Colatino/PicoZoom/src/beta/a1xfour.h

/*
 * The MIT License (MIT)
 *
 * Copyright (c) 2022 André Colatino (https://github.com/Colatino/picozoom)
 *
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
 * This file is part of the PicoZoom project.
 */

#ifndef A1XFOUR_H
#define A1XFOUR_H
#include "effect_model.h"

#define NEFFECTS 199
#define NUM_SLOTS 5
#define NUM_PEDALS 5

#define PEDAL_ID 0x6e
#define N_DELAYS 18
long delay_ids[] = { 138412032, 134217761, 134217937, 134217745, 134217889, 134217872, 134217985, 134217808, 144707584, 134217953, 134217857, 134217905, 134217793, 134218001, 134217921, 134218017, 134217776, 134217969 };

Effect effects[NEFFECTS] = {
  { "Bypass", 0, "", 1, 0, { { 0, 0, 0, 0, "-" }, { 0, 0, 0, 0, "-" }, { 0, 0, 0, 0, "-" }, { 0, 0, 0, 0, "-" }, { 0, 0, 0, 0, "-" }, { 0, 0, 0, 0, "-" }, { 0, 0, 0, 0, "-" }, { 0, 0, 0, 0, "-" } } },
  { "160 Comp", 25165872, "160_COMP.ZD2.BMP", 1, 4, { { 0, 60, 38, 0, "THRSH" }, { 0, 90, 30, 0, "Ratio" }, { 0, 1, 1, 0, "Knee" }, { 0, 100, 80, 0, "VOL" }, { 0, 0, 0, 0, "-" }, { 0, 0, 0, 0, "-" }, { 0, 0, 0, 0, "-" }, { 0, 0, 0, 0, "-" } } },
  { "AG Detune", 104857600, "ACDETUNE.ZD2.BMP", 1, 4, { { 0, 25, 12, 0, "Cent" }, { 0, 50, 34, 0, "PreD" }, { 0, 100, 50, 0, "Tone" }, { 0, 100, 50, 0, "Mix" }, { 0, 0, 0, 0, "-" }, { 0, 0, 0, 0, "-" }, { 0, 0, 0, 0, "-" }, { 0, 0, 0, 0, "-" } } },
  { "Ac TpEcho", 138412032, "AC_TPECH.ZD2.BMP", 1, 4, { { 0, 1005, 350, 0, "Time" }, { 0, 100, 20, 0, "F.B" }, { 0, 100, 50, 0, "Mix" }, { 0, 1, 0, 0, "Tail" }, { 0, 0, 0, 0, "-" }, { 0, 0, 0, 0, "-" }, { 0, 0, 0, 0, "-" }, { 0, 0, 0, 0, "-" } } },
  { "AG Chorus", 104857616, "AC_TRCHO.ZD2.BMP", 1, 4, { { 0, 100, 29, 0, "Speed" }, { 0, 100, 80, 0, "Depth" }, { 0, 100, 100, 0, "Tone" }, { 0, 100, 41, 0, "Mix" }, { 0, 0, 0, 0, "-" }, { 0, 0, 0, 0, "-" }, { 0, 0, 0, 0, "-" }, { 0, 0, 0, 0, "-" } } },
  { "Adv.NR", 27267072, "ADVNR.ZD2.BMP", 1, 4, { { 0, 100, 30, 0, "THRSH" }, { 0, 100, 0, 0, "ATTCK" }, { 0, 100, 0, 0, "Hold" }, { 0, 100, 80, 0, "Decay" }, { 0, 0, 0, 0, "-" }, { 0, 0, 0, 0, "-" }, { 0, 0, 0, 0, "-" }, { 0, 0, 0, 0, "-" } } },
  { "AG PU SEL", 37748737, "AG_PUSL.ZD2.BMP", 1, 1, { { 0, 1, 0, 0, "Type" }, { 0, 0, 0, 0, "-" }, { 0, 0, 0, 0, "-" }, { 0, 0, 0, 0, "-" }, { 0, 0, 0, 0, "-" }, { 0, 0, 0, 0, "-" }, { 0, 0, 0, 0, "-" }, { 0, 0, 0, 0, "-" } } },
  { "Air", 150994960, "AIR.ZD2.BMP", 1, 4, { { 0, 99, 19, 0, "Size" }, { 0, 10, 5, 0, "REF" }, { 0, 100, 60, 0, "Mix" }, { 0, 1, 0, 0, "Tail" }, { 0, 0, 0, 0, "-" }, { 0, 0, 0, 0, "-" }, { 0, 0, 0, 0, "-" }, { 0, 0, 0, 0, "-" } } },
  { "AnalogCho", 100663632, "ANA234CH.ZD2.BMP", 1, 4, { { 0, 100, 52, 0, "Depth" }, { 0, 100, 54, 0, "Rate" }, { 0, 100, 49, 0, "Tone" }, { 0, 100, 82, 0, "Mix" }, { 0, 0, 0, 0, "-" }, { 0, 0, 0, 0, "-" }, { 0, 0, 0, 0, "-" }, { 0, 0, 0, 0, "-" } } },
  { "AnalogDly", 134217761, "ANDLY_3S.ZD2.BMP", 1, 4, { { 0, 3018, 359, 0, "Time" }, { 0, 100, 28, 0, "F.B" }, { 0, 100, 40, 0, "Mix" }, { 0, 1, 0, 0, "Tail" }, { 0, 0, 0, 0, "-" }, { 0, 0, 0, 0, "-" }, { 0, 0, 0, 0, "-" }, { 0, 0, 0, 0, "-" } } },
  { "Anti FB", 50331632, "ANTI_FB.ZD2.BMP", 1, 1, { { 0, 139, 0, 0, "FREQ" }, { 0, 0, 0, 0, "-" }, { 0, 0, 0, 0, "-" }, { 0, 0, 0, 0, "-" }, { 0, 0, 0, 0, "-" }, { 0, 0, 0, 0, "-" }, { 0, 0, 0, 0, "-" }, { 0, 0, 0, 0, "-" } } },
  { "A-Pan DLY", 134217937, "APANDL3S.ZD2.BMP", 2, 7, { { 0, 1512, 222, 0, "Time" }, { 0, 100, 87, 0, "F.B" }, { 0, 100, 53, 0, "Mix" }, { 0, 1, 1, 0, "Link" }, { 0, 52, 26, 0, "Cycle" }, { 0, 50, 50, 0, "Width" }, { 0, 10, 0, 0, "Clip" }, { 0, 0, 0, 0, "-" } } },
  { "SaxAtkFlt", 44041236, "ATK_FLT.ZD2.BMP", 2, 8, { { 0, 9, 7, 0, "Sense" }, { 0, 9, 7, 0, "RESO" }, { 0, 100, 80, 0, "BAL" }, { 0, 2, 0, 0, "SW" }, { 0, 77, 54, 0, "Rate" }, { 0, 3, 0, 0, "Wave" }, { 0, 1, 0, 0, "Range" }, { 0, 100, 80, 0, "VOL" } } },
  { "AutoPan", 117440544, "AUTOPAN.ZD2.BMP", 1, 4, { { 0, 78, 5, 0, "Rate" }, { 0, 50, 50, 0, "Width" }, { 0, 10, 0, 0, "Clip" }, { 0, 100, 80, 0, "VOL" }, { 0, 0, 0, 0, "-" }, { 0, 0, 0, 0, "-" }, { 0, 0, 0, 0, "-" }, { 0, 0, 0, 0, "-" } } },
  { "AutoWah", 33554448, "AUTOWAH.ZD2.BMP", 1, 4, { { 0, 1, 1, 0, "Mode" }, { 0, 9, 7, 0, "Sense" }, { 0, 10, 8, 0, "RESO" }, { 0, 100, 80, 0, "VOL" }, { 0, 0, 0, 0, "-" }, { 0, 0, 0, 0, "-" }, { 0, 0, 0, 0, "-" }, { 0, 0, 0, 0, "-" } } },
  { "Hm A.Wah", 44040546, "AWAH_HM.ZD2.BMP", 1, 4, { { 0, 9, 4, 0, "Sense" }, { 0, 10, 5, 0, "RESO" }, { 0, 100, 0, 0, "Range" }, { 0, 100, 83, 0, "BAL" }, { 0, 0, 0, 0, "-" }, { 0, 0, 0, 0, "-" }, { 0, 0, 0, 0, "-" }, { 0, 0, 0, 0, "-" } } },
  { "Sax A.Wah", 44041234, "AWAH_SAX.ZD2.BMP", 1, 4, { { 0, 9, 4, 0, "Sense" }, { 0, 10, 5, 0, "RESO" }, { 0, 100, 83, 0, "BAL" }, { 0, 1, 0, 0, "INST" }, { 0, 0, 0, 0, "-" }, { 0, 0, 0, 0, "-" }, { 0, 0, 0, 0, "-" }, { 0, 0, 0, 0, "-" } } },
  { "Tp A.Wah", 44041090, "AWAH_TP.ZD2.BMP", 2, 6, { { 0, 9, 4, 0, "Sense" }, { 0, 10, 5, 0, "RESO" }, { 0, 100, 80, 0, "BAL" }, { 0, 10, 5, 0, "THRSH" }, { 0, 10, 5, 0, "Peak" }, { 0, 100, 80, 0, "VOL" }, { 0, 0, 0, 0, "-" }, { 0, 0, 0, 0, "-" } } },
  { "Vn A.Wah", 44040836, "AWAH_VN.ZD2.BMP", 1, 4, { { 0, 19, 15, 0, "Sense" }, { 0, 10, 7, 0, "RESO" }, { 0, 10, 6, 0, "LoMix" }, { 0, 100, 100, 0, "BAL" }, { 0, 0, 0, 0, "-" }, { 0, 0, 0, 0, "-" }, { 0, 0, 0, 0, "-" }, { 0, 0, 0, 0, "-" } } },
  { "A-Filter", 41943088, "A_FILTER.ZD2.BMP", 1, 4, { { 0, 1, 0, 0, "Mode" }, { 0, 9, 7, 0, "Sense" }, { 0, 10, 7, 0, "Peak" }, { 0, 100, 10, 0, "Dry" }, { 0, 0, 0, 0, "-" }, { 0, 0, 0, 0, "-" }, { 0, 0, 0, 0, "-" }, { 0, 0, 0, 0, "-" } } },
  { "Baggs EQ", 37748784, "BAGGSEQ.ZD2.BMP", 2, 8, { { 0, 40, 20, 0, "Bass" }, { 0, 40, 20, 0, "LMidF" }, { 0, 40, 20, 0, "LoMid" }, { 0, 40, 20, 0, "HMidF" }, { 0, 40, 20, 0, "HiMid" }, { 0, 40, 20, 0, "PRSNC" }, { 0, 40, 20, 0, "TRBL" }, { 0, 100, 80, 0, "VOL" } } },
  { "BassWah", 192938000, "BASSWAH.ZD2.BMP", 1, 4, { { 1, 100, 50, 0, "FREQ" }, { 0, 100, 50, 0, "Range" }, { 0, 100, 20, 0, "Dry" }, { 0, 100, 80, 0, "VOL" }, { 0, 0, 0, 0, "-" }, { 0, 0, 0, 0, "-" }, { 0, 0, 0, 0, "-" }, { 0, 0, 0, 0, "-" } } },
  { "BassPhase", 109052032, "BASS_PHA.ZD2.BMP", 1, 4, { { 0, 1, 1, 0, "Color" }, { 0, 100, 100, 0, "Depth" }, { 0, 100, 55, 0, "Rate" }, { 0, 100, 56, 0, "RESO" }, { 0, 0, 0, 0, "-" }, { 0, 0, 0, 0, "-" }, { 0, 0, 0, 0, "-" }, { 0, 0, 0, 0, "-" } } },
  { "Bass Cry", 41943104, "BA_CRY.ZD2.BMP", 1, 4, { { 0, 9, 3, 0, "Range" }, { 0, 10, 9, 0, "RESO" }, { 0, 19, 17, 0, "Sense" }, { 0, 100, 100, 0, "BAL" }, { 0, 0, 0, 0, "-" }, { 0, 0, 0, 0, "-" }, { 0, 0, 0, 0, "-" }, { 0, 0, 0, 0, "-" } } },
  { "BassGEQ", 41943121, "BA_GEQ1U.ZD2.BMP", 2, 8, { { 0, 48, 24, 0, "50" }, { 0, 48, 24, 0, "120" }, { 0, 48, 24, 0, "400" }, { 0, 48, 24, 0, "500" }, { 0, 48, 24, 0, "800" }, { 0, 48, 24, 0, "4.5k" }, { 0, 48, 24, 0, "10k" }, { 0, 100, 80, 0, "VOL" } } },
  { "BassPEQ", 41943152, "BA_PEQ.ZD2.BMP", 1, 4, { { 0, 37, 8, 0, "FREQ" }, { 0, 67, 5, 0, "Q" }, { 0, 80, 40, 0, "Gain" }, { 0, 100, 80, 0, "VOL" }, { 0, 0, 0, 0, "-" }, { 0, 0, 0, 0, "-" }, { 0, 0, 0, 0, "-" }, { 0, 0, 0, 0, "-" } } },
  { "BendCho", 100663616, "BENDCHO.ZD2.BMP", 1, 4, { { 0, 1, 0, 0, "Mode" }, { 0, 100, 40, 0, "Depth" }, { 0, 50, 50, 0, "Time" }, { 0, 100, 100, 0, "BAL" }, { 0, 0, 0, 0, "-" }, { 0, 0, 0, 0, "-" }, { 0, 0, 0, 0, "-" }, { 0, 0, 0, 0, "-" } } },
  { "BlackOpt", 25165840, "BLACKOPT.ZD2.BMP", 1, 4, { { 0, 100, 50, 0, "Comp" }, { 0, 100, 50, 0, "Lo" }, { 0, 100, 50, 0, "Hi" }, { 0, 100, 76, 0, "VOL" }, { 0, 0, 0, 0, "-" }, { 0, 0, 0, 0, "-" }, { 0, 0, 0, 0, "-" }, { 0, 0, 0, 0, "-" } } },
  { "BlackWah", 184549408, "BLCK_WAH.ZD2.BMP", 1, 4, { { 1, 100, 50, 0, "FREQ" }, { 0, 100, 50, 0, "Range" }, { 0, 100, 0, 0, "Dry" }, { 0, 100, 80, 0, "VOL" }, { 0, 0, 0, 0, "-" }, { 0, 0, 0, 0, "-" }, { 0, 0, 0, 0, "-" }, { 0, 0, 0, 0, "-" } } },
  { "Bomber", 117440528, "BOMBER.ZD2.BMP", 1, 4, { { 0, 99, 49, 0, "Decay" }, { 0, 10, 4, 0, "Tone" }, { 0, 100, 30, 0, "Mix" }, { 0, 1, 1, 0, "ON/OFF" }, { 0, 0, 0, 0, "-" }, { 0, 0, 0, 0, "-" }, { 0, 0, 0, 0, "-" }, { 0, 0, 0, 0, "-" } } },
  { "Bone EQ", 37748800, "BONE_EQ.ZD2.BMP", 2, 8, { { 0, 40, 20, 0, "Bass" }, { 0, 40, 20, 0, "Mid F" }, { 0, 40, 20, 0, "Mid" }, { 0, 40, 20, 0, "Hi" }, { 0, 2, 0, 0, "Ntc Q" }, { 0, 40, 20, 0, "Notch" }, { 0, 2, 0, 0, "LoCut" }, { 0, 100, 80, 0, "VOL" } } },
  { "BassA-Wah", 41943056, "B_ATWAH.ZD2.BMP", 1, 4, { { 0, 19, 11, 0, "Sense" }, { 0, 10, 8, 0, "RESO" }, { 0, 100, 50, 0, "Dry" }, { 0, 100, 80, 0, "VOL" }, { 0, 0, 0, 0, "-" }, { 0, 0, 0, 0, "-" }, { 0, 0, 0, 0, "-" }, { 0, 0, 0, 0, "-" } } },
  { "Ba Detune", 109052000, "B_DETUNE.ZD2.BMP", 1, 4, { { 0, 50, 35, 0, "Cent" }, { 0, 50, 0, 0, "PreD" }, { 0, 10, 8, 0, "Tone" }, { 0, 100, 60, 0, "Mix" }, { 0, 0, 0, 0, "-" }, { 0, 0, 0, 0, "-" }, { 0, 0, 0, 0, "-" }, { 0, 0, 0, 0, "-" } } },
  { "Hm Bullet", 44040550, "B_MIC.ZD2.BMP", 1, 4, { { 0, 48, 24, 0, "Low" }, { 0, 48, 24, 0, "MID" }, { 0, 48, 24, 0, "Hi" }, { 0, 100, 80, 0, "VOL" }, { 0, 0, 0, 0, "-" }, { 0, 0, 0, 0, "-" }, { 0, 0, 0, 0, "-" }, { 0, 0, 0, 0, "-" } } },
  { "Ba Octave", 109051984, "B_OCTAVE.ZD2.BMP", 1, 4, { { 0, 100, 80, 0, "Oct" }, { 0, 10, 3, 0, "Lo" }, { 0, 10, 8, 0, "Hi" }, { 0, 100, 100, 0, "Dry" }, { 0, 0, 0, 0, "-" }, { 0, 0, 0, 0, "-" }, { 0, 0, 0, 0, "-" }, { 0, 0, 0, 0, "-" } } },
  { "Ba PDLMnP", 192938048, "B_PDLMNP.ZD2.BMP", 1, 4, { { 1, 100, 0, 0, "Bend" }, { 0, 8, 0, 0, "Color" }, { 0, 10, 10, 0, "Tone" }, { 0, 1, 0, 0, "Mode" }, { 0, 0, 0, 0, "-" }, { 0, 0, 0, 0, "-" }, { 0, 0, 0, 0, "-" }, { 0, 0, 0, 0, "-" } } },
  { "Ba PDLPit", 192938032, "B_PDLPIT.ZD2.BMP", 1, 4, { { 1, 100, 0, 0, "Bend" }, { 0, 8, 0, 0, "Color" }, { 0, 10, 10, 0, "Tone" }, { 0, 1, 0, 0, "Mode" }, { 0, 0, 0, 0, "-" }, { 0, 0, 0, 0, "-" }, { 0, 0, 0, 0, "-" }, { 0, 0, 0, 0, "-" } } },
  { "BaMnPitch", 109052016, "B_PITCH.ZD2.BMP", 1, 4, { { 0, 25, 0, 0, "Shift" }, { 0, 50, 25, 0, "Fine" }, { 0, 10, 7, 0, "Tone" }, { 0, 100, 50, 0, "BAL" }, { 0, 0, 0, 0, "-" }, { 0, 0, 0, 0, "-" }, { 0, 0, 0, 0, "-" }, { 0, 0, 0, 0, "-" } } },
  { "BassStCho", 109051936, "B_ST_CHO.ZD2.BMP", 1, 4, { { 0, 100, 75, 0, "Depth" }, { 0, 49, 26, 0, "Rate" }, { 0, 10, 3, 0, "LoCut" }, { 0, 100, 76, 0, "Mix" }, { 0, 0, 0, 0, "-" }, { 0, 0, 0, 0, "-" }, { 0, 0, 0, 0, "-" }, { 0, 0, 0, 0, "-" } } },
  { "BaVinFLNG", 109051968, "B_VFLNG.ZD2.BMP", 1, 4, { { 0, 100, 47, 0, "Depth" }, { 0, 78, 7, 0, "Rate" }, { 0, 20, 18, 0, "RESO" }, { 0, 10, 1, 0, "LoCut" }, { 0, 0, 0, 0, "-" }, { 0, 0, 0, 0, "-" }, { 0, 0, 0, 0, "-" }, { 0, 0, 0, 0, "-" } } },
  { "Chamber", 150995152, "CHAMBER.ZD2.BMP", 1, 4, { { 0, 200, 24, 0, "PreD" }, { 0, 100, 50, 0, "Decay" }, { 0, 100, 48, 0, "Mix" }, { 0, 1, 1, 0, "Tail" }, { 0, 0, 0, 0, "-" }, { 0, 0, 0, 0, "-" }, { 0, 0, 0, 0, "-" }, { 0, 0, 0, 0, "-" } } },
  { "Hm Chorus", 111149408, "CHOHM.ZD2.BMP", 2, 6, { { 0, 50, 28, 0, "Cent" }, { 0, 100, 18, 0, "Depth" }, { 0, 100, 42, 0, "PreD" }, { 0, 24, 17, 0, "MID" }, { 0, 24, 10, 0, "Hi" }, { 0, 100, 18, 0, "BAL" }, { 0, 0, 0, 0, "-" }, { 0, 0, 0, 0, "-" } } },
  { "Chorus", 100663328, "CHORUS.ZD2.BMP", 1, 4, { { 0, 100, 40, 0, "Depth" }, { 0, 49, 24, 0, "Rate" }, { 0, 10, 7, 0, "Tone" }, { 0, 100, 50, 0, "Mix" }, { 0, 0, 0, 0, "-" }, { 0, 0, 0, 0, "-" }, { 0, 0, 0, 0, "-" }, { 0, 0, 0, 0, "-" } } },
  { "SaxChorus", 111150096, "CHOSAX.ZD2.BMP", 2, 6, { { 0, 50, 28, 0, "Cent" }, { 0, 100, 16, 0, "Depth" }, { 0, 100, 24, 0, "PreD" }, { 0, 24, 15, 0, "MID" }, { 0, 24, 15, 0, "Hi" }, { 0, 100, 50, 0, "BAL" }, { 0, 0, 0, 0, "-" }, { 0, 0, 0, 0, "-" } } },
  { "Tp Chorus", 111149952, "CHOTP.ZD2.BMP", 2, 6, { { 0, 50, 35, 0, "Cent" }, { 0, 100, 53, 0, "Depth" }, { 0, 100, 50, 0, "PreD" }, { 0, 24, 19, 0, "MID" }, { 0, 24, 17, 0, "Hi" }, { 0, 100, 60, 0, "BAL" }, { 0, 0, 0, 0, "-" }, { 0, 0, 0, 0, "-" } } },
  { "Vn Chorus", 111149696, "CHOVN.ZD2.BMP", 2, 6, { { 0, 50, 25, 0, "Cent" }, { 0, 100, 100, 0, "Depth" }, { 0, 100, 62, 0, "PreD" }, { 0, 12, 0, 0, "LoCut" }, { 0, 24, 9, 0, "Hi" }, { 0, 100, 36, 0, "BAL" }, { 0, 0, 0, 0, "-" }, { 0, 0, 0, 0, "-" } } },
  { "ChromeWah", 184549424, "CHRM_WAH.ZD2.BMP", 1, 4, { { 1, 100, 50, 0, "FREQ" }, { 0, 100, 50, 0, "Range" }, { 0, 100, 0, 0, "Dry" }, { 0, 100, 80, 0, "VOL" }, { 0, 0, 0, 0, "-" }, { 0, 0, 0, 0, "-" }, { 0, 0, 0, 0, "-" }, { 0, 0, 0, 0, "-" } } },
  { "Church", 150995104, "CHURCH.ZD2.BMP", 1, 4, { { 0, 200, 96, 0, "PreD" }, { 0, 100, 49, 0, "Decay" }, { 0, 100, 46, 0, "Mix" }, { 0, 1, 0, 0, "Tail" }, { 0, 0, 0, 0, "-" }, { 0, 0, 0, 0, "-" }, { 0, 0, 0, 0, "-" }, { 0, 0, 0, 0, "-" } } },
  { "CloneCho", 100663552, "CLONECHO.ZD2.BMP", 1, 4, { { 0, 1, 1, 0, "Depth" }, { 0, 100, 23, 0, "Rate" }, { 0, 100, 100, 0, "Tone" }, { 0, 100, 100, 0, "Mix" }, { 0, 0, 0, 0, "-" }, { 0, 0, 0, 0, "-" }, { 0, 0, 0, 0, "-" }, { 0, 0, 0, 0, "-" } } },
  { "Comp", 16777232, "COMP.ZD2.BMP", 1, 4, { { 0, 10, 6, 0, "Sense" }, { 0, 1, 0, 0, "ATTCK" }, { 0, 10, 6, 0, "Tone" }, { 0, 100, 80, 0, "VOL" }, { 0, 0, 0, 0, "-" }, { 0, 0, 0, 0, "-" }, { 0, 0, 0, 0, "-" }, { 0, 0, 0, 0, "-" } } },
  { "CoronaTri", 100663601, "CRNTRI3S.ZD2.BMP", 1, 4, { { 0, 100, 100, 0, "Depth" }, { 0, 100, 25, 0, "Speed" }, { 0, 100, 100, 0, "Tone" }, { 0, 100, 100, 0, "Mix" }, { 0, 0, 0, 0, "-" }, { 0, 0, 0, 0, "-" }, { 0, 0, 0, 0, "-" }, { 0, 0, 0, 0, "-" } } },
  { "Cry", 33554480, "CRY.ZD2.BMP", 1, 4, { { 0, 9, 6, 0, "Range" }, { 0, 10, 8, 0, "RESO" }, { 0, 19, 16, 0, "Sense" }, { 0, 100, 100, 0, "BAL" }, { 0, 0, 0, 0, "-" }, { 0, 0, 0, 0, "-" }, { 0, 0, 0, 0, "-" }, { 0, 0, 0, 0, "-" } } },
  { "DYN Comp", 25165920, "DCOMP.ZD2.BMP", 1, 4, { { 0, 10, 6, 0, "Sense" }, { 0, 1, 0, 0, "ATTCK" }, { 0, 100, 50, 0, "Tone" }, { 0, 100, 50, 0, "VOL" }, { 0, 0, 0, 0, "-" }, { 0, 0, 0, 0, "-" }, { 0, 0, 0, 0, "-" }, { 0, 0, 0, 0, "-" } } },
  { "Defret", 125829184, "DEFRET.ZD2.BMP", 1, 4, { { 0, 30, 11, 0, "Sense" }, { 0, 9, 7, 0, "Color" }, { 0, 49, 36, 0, "Tone" }, { 0, 100, 80, 0, "VOL" }, { 0, 0, 0, 0, "-" }, { 0, 0, 0, 0, "-" }, { 0, 0, 0, 0, "-" }, { 0, 0, 0, 0, "-" } } },
  { "Delay", 134217745, "DELAY_3S.ZD2.BMP", 1, 4, { { 0, 3018, 559, 0, "Time" }, { 0, 100, 30, 0, "F.B" }, { 0, 100, 70, 0, "Mix" }, { 0, 1, 0, 0, "Tail" }, { 0, 0, 0, 0, "-" }, { 0, 0, 0, 0, "-" }, { 0, 0, 0, 0, "-" }, { 0, 0, 0, 0, "-" } } },
  { "Detune", 100663456, "DETUNE.ZD2.BMP", 1, 4, { { 0, 50, 35, 0, "Cent" }, { 0, 50, 0, 0, "PreD" }, { 0, 10, 8, 0, "Tone" }, { 0, 100, 52, 0, "Mix" }, { 0, 0, 0, 0, "-" }, { 0, 0, 0, 0, "-" }, { 0, 0, 0, 0, "-" }, { 0, 0, 0, 0, "-" } } },
  { "Vn DIST", 60818048, "DIST_VN.ZD2.BMP", 2, 6, { { 0, 100, 68, 0, "Gain" }, { 0, 100, 100, 0, "BAL" }, { 0, 100, 74, 0, "VOL" }, { 0, 100, 50, 0, "Bass" }, { 0, 100, 50, 0, "MID" }, { 0, 100, 50, 0, "Treble" }, { 0, 0, 0, 0, "-" }, { 0, 0, 0, 0, "-" } } },
  { "BaDePiezo", 37748752, "DPZ_BA.ZD2.BMP", 1, 4, { { 0, 12, 6, 0, "Gain" }, { 0, 1, 0, 0, "Mode" }, { 0, 100, 0, 0, "LoBst" }, { 0, 100, 0, 0, "HiCut" }, { 0, 0, 0, 0, "-" }, { 0, 0, 0, 0, "-" }, { 0, 0, 0, 0, "-" }, { 0, 0, 0, 0, "-" } } },
  { "DryPlate", 161484800, "DRYPLATE.ZD2.BMP", 1, 4, { { 0, 199, 79, 0, "PreD" }, { 0, 100, 34, 0, "Decay" }, { 0, 100, 94, 0, "LoDMP" }, { 0, 100, 20, 0, "Mix" }, { 0, 0, 0, 0, "-" }, { 0, 0, 0, 0, "-" }, { 0, 0, 0, 0, "-" }, { 0, 0, 0, 0, "-" } } },
  { "Dual DLY", 134217889, "DUALDL3S.ZD2.BMP", 2, 8, { { 0, 1503, 500, 0, "TimeA" }, { 0, 110, 50, 0, "F.B A" }, { 0, 1503, 375, 0, "TimeB" }, { 0, 110, 50, 0, "F.B B" }, { 0, 100, 25, 0, "DlyMx" }, { 0, 100, 50, 0, "BAL" }, { 0, 101, 0, 0, "Depth" }, { 0, 50, 25, 0, "Speed" } } },
  { "DualPitch", 111153168, "DUALPIT.ZD2.BMP", 2, 7, { { 0, 25, 7, 0, "ShftA" }, { 0, 12, 9, 0, "ToneA" }, { 0, 100, 60, 0, "VOL A" }, { 0, 25, 0, 0, "ShftB" }, { 0, 12, 9, 0, "ToneB" }, { 0, 100, 80, 0, "VOL B" }, { 0, 100, 100, 0, "Dry" }, { 0, 0, 0, 0, "-" } } },
  { "DualComp", 25165888, "DUAL_CMP.ZD2.BMP", 1, 4, { { 0, 9, 9, 0, "FREQ" }, { 0, 50, 15, 0, "LoCMP" }, { 0, 50, 24, 0, "HiCMP" }, { 0, 100, 75, 0, "VOL" }, { 0, 0, 0, 0, "-" }, { 0, 0, 0, 0, "-" }, { 0, 0, 0, 0, "-" }, { 0, 0, 0, 0, "-" } } },
  { "Duo Phase", 100663665, "DUOPHA1U.ZD2.BMP", 2, 8, { { 0, 99, 62, 0, "DPT A" }, { 0, 77, 5, 0, "RateA" }, { 0, 10, 6, 0, "ResoA" }, { 0, 2, 0, 0, "Link" }, { 0, 99, 36, 0, "DPT B" }, { 0, 51, 46, 0, "RateB" }, { 0, 10, 0, 0, "ResoB" }, { 0, 100, 80, 0, "VOL" } } },
  { "EarlyRef", 150995072, "EARLYREF.ZD2.BMP", 1, 4, { { 0, 29, 14, 0, "Decay" }, { 0, 20, 20, 0, "Shape" }, { 0, 10, 6, 0, "Tone" }, { 0, 100, 50, 0, "Mix" }, { 0, 0, 0, 0, "-" }, { 0, 0, 0, 0, "-" }, { 0, 0, 0, 0, "-" }, { 0, 0, 0, 0, "-" } } },
  { "Ensemble", 111153184, "ENSEMBLE.ZD2.BMP", 1, 4, { { 0, 100, 50, 0, "Depth" }, { 0, 12, 2, 0, "MID" }, { 0, 12, 9, 0, "Hi" }, { 0, 100, 64, 0, "BAL" }, { 0, 0, 0, 0, "-" }, { 0, 0, 0, 0, "-" }, { 0, 0, 0, 0, "-" }, { 0, 0, 0, 0, "-" } } },
  { "EnvPhaser", 111153200, "ENVPHA.ZD2.BMP", 2, 7, { { 0, 3, 0, 0, "Color" }, { 0, 100, 50, 0, "Depth" }, { 0, 100, 50, 0, "RESO" }, { 0, 9, 4, 0, "Sense" }, { 0, 4, 1, 0, "RateL" }, { 0, 4, 1, 0, "RateH" }, { 0, 1, 1, 0, "Curve" }, { 0, 0, 0, 0, "-" } } },
  { "EnvFilter", 41943200, "ENV_FLTR.ZD2.BMP", 1, 4, { { 0, 100, 8, 0, "THRSH" }, { 0, 100, 66, 0, "ATTCK" }, { 0, 1, 0, 0, "Mode" }, { 0, 100, 70, 0, "VOL" }, { 0, 0, 0, 0, "-" }, { 0, 0, 0, 0, "-" }, { 0, 0, 0, 0, "-" }, { 0, 0, 0, 0, "-" } } },
  { "A.Vn GEQ", 44040832, "EQ_AVN.ZD2.BMP", 2, 8, { { 0, 48, 24, 0, "131" }, { 0, 72, 36, 0, "270" }, { 0, 48, 24, 0, "450" }, { 0, 48, 24, 0, "524" }, { 0, 48, 24, 0, "1.4k" }, { 0, 48, 24, 0, "3.0k" }, { 0, 48, 24, 0, "6.0k" }, { 0, 100, 80, 0, "VOL" } } },
  { "E.Vn GEQ", 44040834, "EQ_EVN.ZD2.BMP", 2, 8, { { 0, 48, 24, 0, "131" }, { 0, 48, 24, 0, "220" }, { 0, 48, 24, 0, "450" }, { 0, 48, 24, 0, "800" }, { 0, 48, 24, 0, "2.2k" }, { 0, 48, 24, 0, "3.1k" }, { 0, 48, 24, 0, "7.0k" }, { 0, 100, 80, 0, "VOL" } } },
  { "Hm GEQ", 44040544, "EQ_HARM.ZD2.BMP", 2, 8, { { 0, 48, 24, 0, "60" }, { 0, 48, 24, 0, "250" }, { 0, 48, 24, 0, "400" }, { 0, 48, 24, 0, "700" }, { 0, 48, 24, 0, "1.0k" }, { 0, 48, 24, 0, "2.0k" }, { 0, 48, 24, 0, "4.0k" }, { 0, 100, 80, 0, "VOL" } } },
  { "Sax GEQ", 44041232, "EQ_SAX.ZD2.BMP", 2, 8, { { 0, 48, 24, 0, "200" }, { 0, 48, 24, 0, "400" }, { 0, 48, 24, 0, "640" }, { 0, 48, 24, 0, "1.0k" }, { 0, 48, 24, 0, "2.0k" }, { 0, 48, 24, 0, "3.2k" }, { 0, 48, 24, 0, "5.0k" }, { 0, 100, 80, 0, "VOL" } } },
  { "Tp GEQ", 44041088, "EQ_TP.ZD2.BMP", 2, 8, { { 0, 48, 24, 0, "200" }, { 0, 48, 24, 0, "350" }, { 0, 48, 24, 0, "700" }, { 0, 48, 24, 0, "1.0k" }, { 0, 48, 24, 0, "2.0k" }, { 0, 48, 24, 0, "4.0k" }, { 0, 48, 24, 0, "10.0k" }, { 0, 100, 80, 0, "VOL" } } },
  { "Exciter", 33554608, "EXCITER.ZD2.BMP", 1, 4, { { 0, 100, 0, 0, "Bass" }, { 0, 100, 0, 0, "Treble" }, { 0, 100, 80, 0, "VOL" }, { 0, 1, 0, 0, "ON/OFF" }, { 0, 0, 0, 0, "-" }, { 0, 0, 0, 0, "-" }, { 0, 0, 0, 0, "-" }, { 0, 0, 0, 0, "-" } } },
  { "FD-B4x10", 83886119, "FDB4X10.ZD2.BMP", 1, 4, { { 0, 1, 0, 0, "MIC" }, { 0, 100, 50, 0, "D57:D421" }, { 0, 100, 50, 0, "Hi" }, { 0, 100, 50, 0, "Lo" }, { 0, 0, 0, 0, "-" }, { 0, 0, 0, 0, "-" }, { 0, 0, 0, 0, "-" }, { 0, 0, 0, 0, "-" } } },
  { "FD B-MAN", 67108904, "FDBMAN1U.ZD2.BMP", 2, 7, { { 0, 1, 1, 0, "Input" }, { 0, 110, 30, 0, "Bass" }, { 0, 110, 90, 0, "MID" }, { 0, 110, 40, 0, "Treble" }, { 0, 110, 50, 0, "PRSNC" }, { 0, 110, 30, 0, "Gain" }, { 0, 110, 50, 0, "VOL" }, { 0, 0, 0, 0, "-" } } },
  { "FD DLXR", 67108908, "FDDLXR1U.ZD2.BMP", 2, 7, { { 0, 1, 0, 0, "Input" }, { 0, 90, 33, 0, "Bass" }, { 0, 90, 55, 0, "Treble" }, { 0, 90, 50, 0, "Gain" }, { 0, 90, 90, 0, "VOL" }, { 0, 90, 0, 0, "Depth" }, { 0, 100, 40, 0, "Speed" }, { 0, 0, 0, 0, "-" } } },
  { "FD-DX1x12", 83886122, "FDDX1X12.ZD2.BMP", 1, 4, { { 0, 1, 0, 0, "MIC" }, { 0, 100, 50, 0, "D57:D421" }, { 0, 100, 50, 0, "Hi" }, { 0, 100, 50, 0, "Lo" }, { 0, 0, 0, 0, "-" }, { 0, 0, 0, 0, "-" }, { 0, 0, 0, 0, "-" }, { 0, 0, 0, 0, "-" } } },
  { "FD Spring", 150995040, "FDSPRING.ZD2.BMP", 1, 4, { { 0, 1, 0, 0, "Color" }, { 0, 100, 100, 0, "Lo" }, { 0, 100, 100, 0, "Hi" }, { 0, 100, 50, 0, "Mix" }, { 0, 0, 0, 0, "-" }, { 0, 0, 0, 0, "-" }, { 0, 0, 0, 0, "-" }, { 0, 0, 0, 0, "-" } } },
  { "Fish EQ", 37748768, "FISH_EQ.ZD2.BMP", 1, 4, { { 0, 40, 20, 0, "Low" }, { 0, 40, 20, 0, "Mid" }, { 0, 40, 20, 0, "Hi" }, { 0, 100, 80, 0, "Vol" }, { 0, 0, 0, 0, "-" }, { 0, 0, 0, 0, "-" }, { 0, 0, 0, 0, "-" }, { 0, 0, 0, 0, "-" } } },
  { "FilterDly", 134217872, "FLTRDLY.ZD2.BMP", 1, 4, { { 0, 2014, 499, 0, "Time" }, { 0, 100, 50, 0, "F.B" }, { 0, 100, 90, 0, "Mix" }, { 0, 1, 0, 0, "Tail" }, { 0, 0, 0, 0, "-" }, { 0, 0, 0, 0, "-" }, { 0, 0, 0, 0, "-" }, { 0, 0, 0, 0, "-" } } },
  { "GateRev", 150995168, "GATE_REV.ZD2.BMP", 1, 4, { { 0, 4, 0, 0, "Color" }, { 0, 100, 55, 0, "Decay" }, { 0, 100, 50, 0, "Tone" }, { 0, 100, 60, 0, "BAL" }, { 0, 0, 0, 0, "-" }, { 0, 0, 0, 0, "-" }, { 0, 0, 0, 0, "-" }, { 0, 0, 0, 0, "-" } } },
  { "Glam Comp", 25165936, "GLAMCOMP.ZD2.BMP", 1, 4, { { 0, 100, 91, 0, "Comp" }, { 0, 10, 8, 0, "Shape" }, { 0, 100, 73, 0, "VOL" }, { 0, 100, 51, 0, "DryMx" }, { 0, 0, 0, 0, "-" }, { 0, 0, 0, 0, "-" }, { 0, 0, 0, 0, "-" }, { 0, 0, 0, 0, "-" } } },
  { "GrayComp", 16777312, "GRAYCOMP.ZD2.BMP", 1, 4, { { 0, 100, 63, 0, "SUSTN" }, { 0, 100, 50, 0, "Lo" }, { 0, 100, 50, 0, "Hi" }, { 0, 100, 88, 0, "VOL" }, { 0, 0, 0, 0, "-" }, { 0, 0, 0, 0, "-" }, { 0, 0, 0, 0, "-" }, { 0, 0, 0, 0, "-" } } },
  { "Sax Growl", 111150098, "GROWL.ZD2.BMP", 1, 4, { { 0, 99, 29, 0, "FREQ" }, { 0, 9, 4, 0, "Sense" }, { 0, 10, 10, 0, "Tone" }, { 0, 100, 60, 0, "Mix" }, { 0, 0, 0, 0, "-" }, { 0, 0, 0, 0, "-" }, { 0, 0, 0, 0, "-" }, { 0, 0, 0, 0, "-" } } },
  { "Gt GEQ 7", 33554516, "GTGEQ71U.ZD2.BMP", 2, 8, { { 0, 48, 24, 0, "100" }, { 0, 48, 24, 0, "200" }, { 0, 48, 24, 0, "400" }, { 0, 48, 24, 0, "800" }, { 0, 48, 24, 0, "1.6k" }, { 0, 48, 24, 0, "3.2k" }, { 0, 48, 24, 0, "6.4k" }, { 0, 100, 80, 0, "VOL" } } },
  { "Gt GEQ", 33554513, "GT_GEQ1U.ZD2.BMP", 2, 7, { { 0, 48, 24, 0, "160" }, { 0, 48, 24, 0, "400" }, { 0, 48, 24, 0, "800" }, { 0, 48, 24, 0, "3.2k" }, { 0, 48, 24, 0, "6.4k" }, { 0, 48, 24, 0, "12k" }, { 0, 100, 80, 0, "VOL" }, { 0, 0, 0, 0, "-" } } },
  { "Hall", 150994992, "HALL.ZD2.BMP", 1, 4, { { 0, 99, 48, 0, "PreD" }, { 0, 29, 9, 0, "Decay" }, { 0, 100, 46, 0, "Mix" }, { 0, 1, 0, 0, "Tail" }, { 0, 0, 0, 0, "-" }, { 0, 0, 0, 0, "-" }, { 0, 0, 0, 0, "-" }, { 0, 0, 0, 0, "-" } } },
  { "Hm Preamp", 44040548, "HARM_PRE.ZD2.BMP", 1, 4, { { 0, 100, 50, 0, "Gain" }, { 0, 48, 24, 0, "Low" }, { 0, 48, 24, 0, "MID" }, { 0, 48, 24, 0, "Hi" }, { 0, 0, 0, 0, "-" }, { 0, 0, 0, 0, "-" }, { 0, 0, 0, 0, "-" }, { 0, 0, 0, 0, "-" } } },
  { "HD Hall", 150995008, "HD_HALL.ZD2.BMP", 1, 4, { { 0, 199, 80, 0, "PreD" }, { 0, 100, 45, 0, "Decay" }, { 0, 100, 62, 0, "Mix" }, { 0, 1, 0, 0, "Tail" }, { 0, 0, 0, 0, "-" }, { 0, 0, 0, 0, "-" }, { 0, 0, 0, 0, "-" }, { 0, 0, 0, 0, "-" } } },
  { "High EQ", 41943189, "HIGH_EQ.ZD2.BMP", 1, 4, { { 0, 1, 0, 0, "Type" }, { 0, 55, 16, 0, "FREQ" }, { 0, 48, 36, 0, "Gain" }, { 0, 100, 80, 0, "VOL" }, { 0, 0, 0, 0, "-" }, { 0, 0, 0, 0, "-" }, { 0, 0, 0, 0, "-" }, { 0, 0, 0, 0, "-" } } },
  { "HotSpice", 117440592, "HOTSPICE.ZD2.BMP", 1, 4, { { 0, 100, 11, 0, "Bend" }, { 0, 100, 57, 0, "Buzz" }, { 0, 100, 36, 0, "+1oct" }, { 0, 100, 80, 0, "VOL" }, { 0, 0, 0, 0, "-" }, { 0, 0, 0, 0, "-" }, { 0, 0, 0, 0, "-" }, { 0, 0, 0, 0, "-" } } },
  { "HPS", 100663504, "HPS.ZD2.BMP", 1, 4, { { 0, 9, 6, 0, "Scale" }, { 0, 11, 0, 0, "Key" }, { 0, 10, 6, 0, "Tone" }, { 0, 100, 70, 0, "Mix" }, { 0, 0, 0, 0, "-" }, { 0, 0, 0, 0, "-" }, { 0, 0, 0, 0, "-" }, { 0, 0, 0, 0, "-" } } },
  { "ICE Delay", 134217985, "ICEDLY3S.ZD2.BMP", 1, 4, { { 0, 30, 28, 0, "INTVL" }, { 0, 931, 928, 0, "Time" }, { 0, 100, 46, 0, "F.B" }, { 0, 100, 36, 0, "Mix" }, { 0, 0, 0, 0, "-" }, { 0, 0, 0, 0, "-" }, { 0, 0, 0, 0, "-" }, { 0, 0, 0, 0, "-" } } },
  { "LFO FLTR", 33554640, "LFO_FLTR.ZD2.BMP", 1, 4, { { 0, 100, 100, 0, "Depth" }, { 0, 77, 57, 0, "Rate" }, { 0, 10, 8, 0, "RESO" }, { 0, 3, 0, 0, "Wave" }, { 0, 0, 0, 0, "-" }, { 0, 0, 0, 0, "-" }, { 0, 0, 0, 0, "-" }, { 0, 0, 0, 0, "-" } } },
  { "LMT-76", 25165856, "LMT1176.ZD2.BMP", 1, 4, { { 0, 80, 40, 0, "Input" }, { 0, 3, 0, 0, "Ratio" }, { 0, 60, 10, 0, "REL" }, { 0, 80, 38, 0, "Output" }, { 0, 0, 0, 0, "-" }, { 0, 0, 0, 0, "-" }, { 0, 0, 0, 0, "-" }, { 0, 0, 0, 0, "-" } } },
  { "LowPassFL", 33554592, "LOWPASSF.ZD2.BMP", 1, 4, { { 0, 100, 56, 0, "FREQ" }, { 0, 201, 50, 0, "Sense" }, { 0, 21, 3, 0, "RESO" }, { 0, 100, 100, 0, "BAL" }, { 0, 0, 0, 0, "-" }, { 0, 0, 0, 0, "-" }, { 0, 0, 0, 0, "-" }, { 0, 0, 0, 0, "-" } } },
  { "Low EQ", 41943184, "LOW_EQ.ZD2.BMP", 1, 4, { { 0, 1, 0, 0, "Type" }, { 0, 55, 10, 0, "FREQ" }, { 0, 48, 36, 0, "Gain" }, { 0, 100, 80, 0, "VOL" }, { 0, 0, 0, 0, "-" }, { 0, 0, 0, 0, "-" }, { 0, 0, 0, 0, "-" }, { 0, 0, 0, 0, "-" } } },
  { "LoopRoll", 117440577, "LPROLL3S.ZD2.BMP", 1, 4, { { 0, 3006, 2992, 0, "Time" }, { 0, 75, 75, 0, "Duty" }, { 0, 100, 100, 0, "BAL" }, { 0, 1, 1, 0, "ON/OFF" }, { 0, 0, 0, 0, "-" }, { 0, 0, 0, 0, "-" }, { 0, 0, 0, 0, "-" }, { 0, 0, 0, 0, "-" } } },
  { "MB Comp", 25165904, "MB_COMP.ZD2.BMP", 1, 4, { { 0, 100, 70, 0, "Comp" }, { 0, 100, 50, 0, "LoTHR" }, { 0, 100, 50, 0, "HiTHR" }, { 0, 100, 25, 0, "VOL" }, { 0, 0, 0, 0, "-" }, { 0, 0, 0, 0, "-" }, { 0, 0, 0, 0, "-" }, { 0, 0, 0, 0, "-" } } },
  { "12Strings", 71303568, "MDL_12ST.ZD2.BMP", 1, 4, { { 0, 48, 24, 0, "Gain" }, { 0, 100, 50, 0, "Bass" }, { 0, 100, 50, 0, "MID" }, { 0, 100, 50, 0, "Treble" }, { 0, 0, 0, 0, "-" }, { 0, 0, 0, 0, "-" }, { 0, 0, 0, 0, "-" }, { 0, 0, 0, 0, "-" } } },
  { "314ce", 71303472, "MDL_314.ZD2.BMP", 1, 4, { { 0, 48, 24, 0, "Gain" }, { 0, 100, 50, 0, "Bass" }, { 0, 100, 50, 0, "MID" }, { 0, 100, 50, 0, "Treble" }, { 0, 0, 0, 0, "-" }, { 0, 0, 0, 0, "-" }, { 0, 0, 0, 0, "-" }, { 0, 0, 0, 0, "-" } } },
  { "Adamas", 71303520, "MDL_ADMS.ZD2.BMP", 1, 4, { { 0, 48, 24, 0, "Gain" }, { 0, 100, 50, 0, "Bass" }, { 0, 100, 50, 0, "MID" }, { 0, 100, 50, 0, "Treble" }, { 0, 0, 0, 0, "-" }, { 0, 0, 0, 0, "-" }, { 0, 0, 0, 0, "-" }, { 0, 0, 0, 0, "-" } } },
  { "Adv.Jumbo", 71303344, "MDL_ADVJ.ZD2.BMP", 1, 4, { { 0, 48, 24, 0, "Gain" }, { 0, 100, 50, 0, "Bass" }, { 0, 100, 50, 0, "MID" }, { 0, 100, 50, 0, "Treble" }, { 0, 0, 0, 0, "-" }, { 0, 0, 0, 0, "-" }, { 0, 0, 0, 0, "-" }, { 0, 0, 0, 0, "-" } } },
  { "D-18", 71303184, "MDL_D18.ZD2.BMP", 1, 4, { { 0, 48, 24, 0, "Gain" }, { 0, 100, 50, 0, "Bass" }, { 0, 100, 50, 0, "MID" }, { 0, 100, 50, 0, "Treble" }, { 0, 0, 0, 0, "-" }, { 0, 0, 0, 0, "-" }, { 0, 0, 0, 0, "-" }, { 0, 0, 0, 0, "-" } } },
  { "D-28", 71303168, "MDL_D28.ZD2.BMP", 1, 4, { { 0, 48, 24, 0, "Gain" }, { 0, 100, 50, 0, "Bass" }, { 0, 100, 50, 0, "MID" }, { 0, 100, 50, 0, "Treble" }, { 0, 0, 0, 0, "-" }, { 0, 0, 0, 0, "-" }, { 0, 0, 0, 0, "-" }, { 0, 0, 0, 0, "-" } } },
  { "D-45", 71303200, "MDL_D45.ZD2.BMP", 1, 4, { { 0, 48, 24, 0, "Gain" }, { 0, 100, 50, 0, "Bass" }, { 0, 100, 50, 0, "MID" }, { 0, 100, 50, 0, "Treble" }, { 0, 0, 0, 0, "-" }, { 0, 0, 0, 0, "-" }, { 0, 0, 0, 0, "-" }, { 0, 0, 0, 0, "-" } } },
  { "Dove", 71303392, "MDL_DOVE.ZD2.BMP", 1, 4, { { 0, 48, 24, 0, "Gain" }, { 0, 100, 50, 0, "Bass" }, { 0, 100, 50, 0, "MID" }, { 0, 100, 50, 0, "Treble" }, { 0, 0, 0, 0, "-" }, { 0, 0, 0, 0, "-" }, { 0, 0, 0, 0, "-" }, { 0, 0, 0, 0, "-" } } },
  { "F-55", 71303424, "MDL_F55.ZD2.BMP", 1, 4, { { 0, 48, 24, 0, "Gain" }, { 0, 100, 50, 0, "Bass" }, { 0, 100, 50, 0, "MID" }, { 0, 100, 50, 0, "Treble" }, { 0, 0, 0, 0, "-" }, { 0, 0, 0, 0, "-" }, { 0, 0, 0, 0, "-" }, { 0, 0, 0, 0, "-" } } },
  { "HumBird", 71303376, "MDL_HB.ZD2.BMP", 1, 4, { { 0, 48, 24, 0, "Gain" }, { 0, 100, 50, 0, "Bass" }, { 0, 100, 50, 0, "MID" }, { 0, 100, 50, 0, "Treble" }, { 0, 0, 0, 0, "-" }, { 0, 0, 0, 0, "-" }, { 0, 0, 0, 0, "-" }, { 0, 0, 0, 0, "-" } } },
  { "J-160E", 71303360, "MDL_J160.ZD2.BMP", 1, 4, { { 0, 48, 24, 0, "Gain" }, { 0, 100, 50, 0, "Bass" }, { 0, 100, 50, 0, "MID" }, { 0, 100, 50, 0, "Treble" }, { 0, 0, 0, 0, "-" }, { 0, 0, 0, 0, "-" }, { 0, 0, 0, 0, "-" }, { 0, 0, 0, 0, "-" } } },
  { "J-45", 71303328, "MDL_J45.ZD2.BMP", 1, 4, { { 0, 48, 24, 0, "Gain" }, { 0, 100, 50, 0, "Bass" }, { 0, 100, 50, 0, "MID" }, { 0, 100, 50, 0, "Treble" }, { 0, 0, 0, 0, "-" }, { 0, 0, 0, 0, "-" }, { 0, 0, 0, 0, "-" }, { 0, 0, 0, 0, "-" } } },
  { "LG-0", 71303456, "MDL_LG0.ZD2.BMP", 1, 4, { { 0, 48, 24, 0, "Gain" }, { 0, 100, 50, 0, "Bass" }, { 0, 100, 50, 0, "MID" }, { 0, 100, 50, 0, "Treble" }, { 0, 0, 0, 0, "-" }, { 0, 0, 0, 0, "-" }, { 0, 0, 0, 0, "-" }, { 0, 0, 0, 0, "-" } } },
  { "LG-2", 71303440, "MDL_LG2.ZD2.BMP", 1, 4, { { 0, 48, 24, 0, "Gain" }, { 0, 100, 50, 0, "Bass" }, { 0, 100, 50, 0, "MID" }, { 0, 100, 50, 0, "Treble" }, { 0, 0, 0, 0, "-" }, { 0, 0, 0, 0, "-" }, { 0, 0, 0, 0, "-" }, { 0, 0, 0, 0, "-" } } },
  { "Legend", 71303536, "MDL_LGN.ZD2.BMP", 1, 4, { { 0, 48, 24, 0, "Gain" }, { 0, 100, 50, 0, "Bass" }, { 0, 100, 50, 0, "MID" }, { 0, 100, 50, 0, "Treble" }, { 0, 0, 0, 0, "-" }, { 0, 0, 0, 0, "-" }, { 0, 0, 0, 0, "-" }, { 0, 0, 0, 0, "-" } } },
  { "LL36", 71303488, "MDL_LL36.ZD2.BMP", 1, 4, { { 0, 48, 24, 0, "Gain" }, { 0, 100, 50, 0, "Bass" }, { 0, 100, 50, 0, "MID" }, { 0, 100, 50, 0, "Treble" }, { 0, 0, 0, 0, "-" }, { 0, 0, 0, 0, "-" }, { 0, 0, 0, 0, "-" }, { 0, 0, 0, 0, "-" } } },
  { "LL66", 71303504, "MDL_LL66.ZD2.BMP", 1, 4, { { 0, 48, 24, 0, "Gain" }, { 0, 100, 50, 0, "Bass" }, { 0, 100, 50, 0, "MID" }, { 0, 100, 50, 0, "Treble" }, { 0, 0, 0, 0, "-" }, { 0, 0, 0, 0, "-" }, { 0, 0, 0, 0, "-" }, { 0, 0, 0, 0, "-" } } },
  { "Nylon", 71303552, "MDL_NYLN.ZD2.BMP", 1, 4, { { 0, 48, 24, 0, "Gain" }, { 0, 100, 50, 0, "Bass" }, { 0, 100, 50, 0, "MID" }, { 0, 100, 50, 0, "Treble" }, { 0, 0, 0, 0, "-" }, { 0, 0, 0, 0, "-" }, { 0, 0, 0, 0, "-" }, { 0, 0, 0, 0, "-" } } },
  { "OOO-18", 71303232, "MDL_O318.ZD2.BMP", 1, 4, { { 0, 48, 24, 0, "Gain" }, { 0, 100, 50, 0, "Bass" }, { 0, 100, 50, 0, "MID" }, { 0, 100, 50, 0, "Treble" }, { 0, 0, 0, 0, "-" }, { 0, 0, 0, 0, "-" }, { 0, 0, 0, 0, "-" }, { 0, 0, 0, 0, "-" } } },
  { "OOO-28", 71303216, "MDL_O328.ZD2.BMP", 1, 4, { { 0, 48, 24, 0, "Gain" }, { 0, 100, 50, 0, "Bass" }, { 0, 100, 50, 0, "MID" }, { 0, 100, 50, 0, "Treble" }, { 0, 0, 0, 0, "-" }, { 0, 0, 0, 0, "-" }, { 0, 0, 0, 0, "-" }, { 0, 0, 0, 0, "-" } } },
  { "OM-18", 71303264, "MDL_OM18.ZD2.BMP", 1, 4, { { 0, 48, 24, 0, "Gain" }, { 0, 100, 50, 0, "Bass" }, { 0, 100, 50, 0, "MID" }, { 0, 100, 50, 0, "Treble" }, { 0, 0, 0, 0, "-" }, { 0, 0, 0, 0, "-" }, { 0, 0, 0, 0, "-" }, { 0, 0, 0, 0, "-" } } },
  { "OM-28", 71303248, "MDL_OM28.ZD2.BMP", 1, 4, { { 0, 48, 24, 0, "Gain" }, { 0, 100, 50, 0, "Bass" }, { 0, 100, 50, 0, "MID" }, { 0, 100, 50, 0, "Treble" }, { 0, 0, 0, 0, "-" }, { 0, 0, 0, 0, "-" }, { 0, 0, 0, 0, "-" }, { 0, 0, 0, 0, "-" } } },
  { "OM-42", 71303280, "MDL_OM42.ZD2.BMP", 1, 4, { { 0, 48, 24, 0, "Gain" }, { 0, 100, 50, 0, "Bass" }, { 0, 100, 50, 0, "MID" }, { 0, 100, 50, 0, "Treble" }, { 0, 0, 0, 0, "-" }, { 0, 0, 0, 0, "-" }, { 0, 0, 0, 0, "-" }, { 0, 0, 0, 0, "-" } } },
  { "OO-18", 71303312, "MDL_OO18.ZD2.BMP", 1, 4, { { 0, 48, 24, 0, "Gain" }, { 0, 100, 50, 0, "Bass" }, { 0, 100, 50, 0, "MID" }, { 0, 100, 50, 0, "Treble" }, { 0, 0, 0, 0, "-" }, { 0, 0, 0, 0, "-" }, { 0, 0, 0, 0, "-" }, { 0, 0, 0, 0, "-" } } },
  { "OO-21", 71303296, "MDL_OO21.ZD2.BMP", 1, 4, { { 0, 48, 24, 0, "Gain" }, { 0, 100, 50, 0, "Bass" }, { 0, 100, 50, 0, "MID" }, { 0, 100, 50, 0, "Treble" }, { 0, 0, 0, 0, "-" }, { 0, 0, 0, 0, "-" }, { 0, 0, 0, 0, "-" }, { 0, 0, 0, 0, "-" } } },
  { "Resonator", 71303584, "MDL_RESO.ZD2.BMP", 1, 4, { { 0, 48, 24, 0, "Gain" }, { 0, 100, 50, 0, "Bass" }, { 0, 100, 50, 0, "MID" }, { 0, 100, 50, 0, "Treble" }, { 0, 0, 0, 0, "-" }, { 0, 0, 0, 0, "-" }, { 0, 0, 0, 0, "-" }, { 0, 0, 0, 0, "-" } } },
  { "SJ-200", 71303408, "MDL_SJ20.ZD2.BMP", 1, 4, { { 0, 48, 24, 0, "Gain" }, { 0, 100, 50, 0, "Bass" }, { 0, 100, 50, 0, "MID" }, { 0, 100, 50, 0, "Treble" }, { 0, 0, 0, 0, "-" }, { 0, 0, 0, 0, "-" }, { 0, 0, 0, 0, "-" }, { 0, 0, 0, 0, "-" } } },
  { "UprightBa", 71303600, "MDL_UPBS.ZD2.BMP", 1, 4, { { 0, 48, 24, 0, "Gain" }, { 0, 100, 50, 0, "Bass" }, { 0, 100, 50, 0, "MID" }, { 0, 100, 50, 0, "Treble" }, { 0, 0, 0, 0, "-" }, { 0, 0, 0, 0, "-" }, { 0, 0, 0, 0, "-" }, { 0, 0, 0, 0, "-" } } },
  { "ModDelay", 134217808, "MODDELAY.ZD2.BMP", 1, 4, { { 0, 2014, 499, 0, "Time" }, { 0, 100, 50, 0, "F.B" }, { 0, 100, 62, 0, "Mix" }, { 0, 1, 0, 0, "Tail" }, { 0, 0, 0, 0, "-" }, { 0, 0, 0, 0, "-" }, { 0, 0, 0, 0, "-" }, { 0, 0, 0, 0, "-" } } },
  { "ModReverb", 155189248, "MOD_REV.ZD2.BMP", 1, 4, { { 0, 100, 38, 0, "Depth" }, { 0, 29, 19, 0, "Decay" }, { 0, 100, 45, 0, "Mix" }, { 0, 1, 0, 0, "Tail" }, { 0, 0, 0, 0, "-" }, { 0, 0, 0, 0, "-" }, { 0, 0, 0, 0, "-" }, { 0, 0, 0, 0, "-" } } },
  { "MonoPitch", 100663488, "MONOPITC.ZD2.BMP", 1, 4, { { 0, 25, 0, 0, "Shift" }, { 0, 50, 25, 0, "Fine" }, { 0, 10, 6, 0, "Tone" }, { 0, 100, 50, 0, "BAL" }, { 0, 0, 0, 0, "-" }, { 0, 0, 0, 0, "-" }, { 0, 0, 0, 0, "-" }, { 0, 0, 0, 0, "-" } } },
  { "MuteSW", 16777296, "MUTESW.ZD2.BMP", 1, 4, { { 0, 100, 13, 0, "Edge" }, { 0, 100, 100, 0, "Speed" }, { 0, 1, 0, 0, "INVRT" }, { 0, 2, 1, 0, "ON/OFF" }, { 0, 0, 0, 0, "-" }, { 0, 0, 0, 0, "-" }, { 0, 0, 0, 0, "-" }, { 0, 0, 0, 0, "-" } } },
  { "NoiseGate", 16777328, "N_GATE.ZD2.BMP", 1, 4, { { 0, 1, 1, 0, "DETCT" }, { 0, 100, 100, 0, "Depth" }, { 0, 100, 54, 0, "THRSH" }, { 0, 100, 0, 0, "Decay" }, { 0, 0, 0, 0, "-" }, { 0, 0, 0, 0, "-" }, { 0, 0, 0, 0, "-" }, { 0, 0, 0, 0, "-" } } },
  { "Octave", 100663424, "OCTAVE.ZD2.BMP", 1, 4, { { 0, 100, 80, 0, "OCT1" }, { 0, 100, 15, 0, "OCT2" }, { 0, 10, 8, 0, "Tone" }, { 0, 100, 100, 0, "Dry" }, { 0, 0, 0, 0, "-" }, { 0, 0, 0, 0, "-" }, { 0, 0, 0, 0, "-" }, { 0, 0, 0, 0, "-" } } },
  { "OptComp", 16777344, "OPTCOMP.ZD2.BMP", 1, 4, { { 0, 10, 7, 0, "Drive" }, { 0, 100, 50, 0, "Lo" }, { 0, 100, 50, 0, "Hi" }, { 0, 100, 60, 0, "VOL" }, { 0, 0, 0, 0, "-" }, { 0, 0, 0, 0, "-" }, { 0, 0, 0, 0, "-" }, { 0, 0, 0, 0, "-" } } },
  { "OSC Echo", 184549569, "OSCECH3S.ZD2.BMP", 1, 4, { { 1, 100, 0, 0, "OSC" }, { 0, 481, 311, 0, "T-Min" }, { 0, 481, 81, 0, "T-Max" }, { 0, 100, 80, 0, "Mix" }, { 0, 0, 0, 0, "-" }, { 0, 0, 0, 0, "-" }, { 0, 0, 0, 0, "-" }, { 0, 0, 0, 0, "-" } } },
  { "Output VP", 201326576, "OUT_VP.ZD2.BMP", 1, 1, { { 0, 5075, 4947, 0, "-" }, { 0, 0, 0, 0, "-" }, { 0, 0, 0, 0, "-" }, { 0, 0, 0, 0, "-" }, { 0, 0, 0, 0, "-" }, { 0, 0, 0, 0, "-" }, { 0, 0, 0, 0, "-" }, { 0, 0, 0, 0, "-" } } },
  { "ParaEQ", 33554544, "PARAEQ.ZD2.BMP", 1, 4, { { 0, 30, 8, 0, "FREQ" }, { 0, 67, 1, 0, "Q" }, { 0, 48, 24, 0, "Gain" }, { 0, 100, 80, 0, "VOL" }, { 0, 0, 0, 0, "-" }, { 0, 0, 0, 0, "-" }, { 0, 0, 0, 0, "-" }, { 0, 0, 0, 0, "-" } } },
  { "ParaEQx2", 33554545, "PARAEQ2.ZD2.BMP", 2, 7, { { 0, 30, 8, 0, "Freq1" }, { 0, 5, 1, 0, "Q1" }, { 0, 24, 12, 0, "Gain1" }, { 0, 30, 15, 0, "Freq2" }, { 0, 5, 1, 0, "Q2" }, { 0, 24, 12, 0, "Gain2" }, { 0, 100, 80, 0, "Level" }, { 0, 0, 0, 0, "-" } } },
  { "PDL Delay", 184549537, "PDLDLY3S.ZD2.BMP", 1, 4, { { 1, 100, 100, 0, "InLvl" }, { 0, 3018, 359, 0, "Time" }, { 0, 100, 40, 0, "F.B" }, { 0, 100, 100, 0, "Mix" }, { 0, 0, 0, 0, "-" }, { 0, 0, 0, 0, "-" }, { 0, 0, 0, 0, "-" }, { 0, 0, 0, 0, "-" } } },
  { "PDL Roto", 184549601, "PDLROT3S.ZD2.BMP", 1, 4, { { 1, 1, 0, 0, "Mode" }, { 0, 100, 20, 0, "Drive" }, { 0, 100, 50, 0, "BAL" }, { 0, 100, 80, 0, "VOL" }, { 0, 0, 0, 0, "-" }, { 0, 0, 0, 0, "-" }, { 0, 0, 0, 0, "-" }, { 0, 0, 0, 0, "-" } } },
  { "P-BitCRSH", 184549616, "PDL_BITC.ZD2.BMP", 1, 4, { { 1, 50, 2, 0, "SMPL" }, { 0, 13, 5, 0, "Bit" }, { 0, 10, 8, 0, "Tone" }, { 0, 100, 90, 0, "BAL" }, { 0, 0, 0, 0, "-" }, { 0, 0, 0, 0, "-" }, { 0, 0, 0, 0, "-" }, { 0, 0, 0, 0, "-" } } },
  { "PDL Drive", 184549504, "PDL_DRV.ZD2.BMP", 1, 4, { { 1, 100, 50, 0, "Gain" }, { 0, 100, 74, 0, "Tone" }, { 0, 100, 48, 0, "PRSNC" }, { 0, 100, 61, 0, "VOL" }, { 0, 0, 0, 0, "-" }, { 0, 0, 0, 0, "-" }, { 0, 0, 0, 0, "-" }, { 0, 0, 0, 0, "-" } } },
  { "PDL FLNGR", 184549632, "PDL_FLNG.ZD2.BMP", 1, 4, { { 1, 100, 50, 0, "FREQ" }, { 0, 20, 18, 0, "RESO" }, { 0, 10, 8, 0, "HiDMP" }, { 0, 100, 65, 0, "Mix" }, { 0, 0, 0, 0, "-" }, { 0, 0, 0, 0, "-" }, { 0, 0, 0, 0, "-" }, { 0, 0, 0, 0, "-" } } },
  { "PDL MnPit", 184549472, "PDL_MNPT.ZD2.BMP", 1, 4, { { 1, 100, 0, 0, "Bend" }, { 0, 8, 0, 0, "Color" }, { 0, 10, 10, 0, "Tone" }, { 0, 1, 0, 0, "Mode" }, { 0, 0, 0, 0, "-" }, { 0, 0, 0, 0, "-" }, { 0, 0, 0, 0, "-" }, { 0, 0, 0, 0, "-" } } },
  { "PDL PHSR", 184549520, "PDL_PHA.ZD2.BMP", 1, 4, { { 1, 49, 11, 0, "Rate" }, { 0, 100, 100, 0, "Depth" }, { 0, 100, 50, 0, "RESO" }, { 0, 3, 3, 0, "Color" }, { 0, 0, 0, 0, "-" }, { 0, 0, 0, 0, "-" }, { 0, 0, 0, 0, "-" }, { 0, 0, 0, 0, "-" } } },
  { "PDL Pitch", 184549456, "PDL_PIT.ZD2.BMP", 1, 4, { { 1, 100, 0, 0, "Bend" }, { 0, 8, 0, 0, "Color" }, { 0, 10, 10, 0, "Tone" }, { 0, 1, 0, 0, "Mode" }, { 0, 0, 0, 0, "-" }, { 0, 0, 0, 0, "-" }, { 0, 0, 0, 0, "-" }, { 0, 0, 0, 0, "-" } } },
  { "PDL Reso", 192938016, "PDL_RESO.ZD2.BMP", 1, 4, { { 1, 49, 11, 0, "FREQ" }, { 0, 10, 7, 0, "RESO" }, { 0, 100, 50, 0, "Dry" }, { 0, 100, 92, 0, "VOL" }, { 0, 0, 0, 0, "-" }, { 0, 0, 0, 0, "-" }, { 0, 0, 0, 0, "-" }, { 0, 0, 0, 0, "-" } } },
  { "PDL Rev", 184549552, "PDL_REV.ZD2.BMP", 1, 4, { { 1, 100, 100, 0, "InLvl" }, { 0, 99, 48, 0, "PreD" }, { 0, 29, 14, 0, "Decay" }, { 0, 100, 80, 0, "Mix" }, { 0, 0, 0, 0, "-" }, { 0, 0, 0, 0, "-" }, { 0, 0, 0, 0, "-" }, { 0, 0, 0, 0, "-" } } },
  { "PDL Vibe", 184549488, "PDL_VIBE.ZD2.BMP", 1, 4, { { 1, 50, 25, 0, "Speed" }, { 0, 100, 60, 0, "Depth" }, { 0, 1, 1, 0, "Mode" }, { 0, 100, 80, 0, "VOL" }, { 0, 0, 0, 0, "-" }, { 0, 0, 0, 0, "-" }, { 0, 0, 0, 0, "-" }, { 0, 0, 0, 0, "-" } } },
  { "PDL Vol", 184549392, "PDL_VOL.ZD2.BMP", 1, 4, { { 1, 100, 100, 0, "VOL" }, { 0, 100, 0, 0, "Min" }, { 0, 100, 100, 0, "Max" }, { 0, 1, 0, 0, "Curve" }, { 0, 0, 0, 0, "-" }, { 0, 0, 0, 0, "-" }, { 0, 0, 0, 0, "-" }, { 0, 0, 0, 0, "-" } } },
  { "PercusDly", 144707584, "PERCDLY.ZD2.BMP", 2, 8, { { 0, 1018, 359, 0, "Time" }, { 0, 100, 28, 0, "F.B" }, { 0, 100, 40, 0, "Mix" }, { 0, 10, 10, 0, "Tone" }, { 0, 10, 5, 0, "Sense" }, { 0, 10, 8, 0, "ATTCK" }, { 0, 100, 50, 0, "Comp" }, { 0, 1, 0, 0, "Tail" } } },
  { "PhaseDly", 134217953, "PHASDL1U.ZD2.BMP", 2, 8, { { 0, 2014, 2006, 0, "Time" }, { 0, 100, 24, 0, "F.B" }, { 0, 100, 56, 0, "Mix" }, { 0, 1, 1, 0, "Tail" }, { 0, 3, 2, 0, "Color" }, { 0, 100, 100, 0, "Depth" }, { 0, 77, 59, 0, "Rate" }, { 0, 100, 48, 0, "Reso" } } },
  { "Phaser", 100663360, "PHASER.ZD2.BMP", 1, 4, { { 0, 3, 3, 0, "Color" }, { 0, 100, 100, 0, "Depth" }, { 0, 77, 11, 0, "Rate" }, { 0, 100, 50, 0, "RESO" }, { 0, 0, 0, 0, "-" }, { 0, 0, 0, 0, "-" }, { 0, 0, 0, 0, "-" }, { 0, 0, 0, 0, "-" } } },
  { "PH+Dist", 125829200, "PH_DIST.ZD2.BMP", 1, 4, { { 0, 3, 3, 0, "Mode" }, { 0, 50, 3, 0, "Rate" }, { 0, 10, 10, 0, "RESO" }, { 0, 100, 80, 0, "VOL" }, { 0, 0, 0, 0, "-" }, { 0, 0, 0, 0, "-" }, { 0, 0, 0, 0, "-" }, { 0, 0, 0, 0, "-" } } },
  { "PitchSHFT", 100663472, "PITCHSHF.ZD2.BMP", 1, 4, { { 0, 25, 19, 0, "Shift" }, { 0, 50, 25, 0, "Fine" }, { 0, 10, 7, 0, "Tone" }, { 0, 100, 40, 0, "BAL" }, { 0, 0, 0, 0, "-" }, { 0, 0, 0, 0, "-" }, { 0, 0, 0, 0, "-" }, { 0, 0, 0, 0, "-" } } },
  { "Plate", 150995056, "PLATEREV.ZD2.BMP", 1, 4, { { 0, 199, 8, 0, "PreD" }, { 0, 100, 52, 0, "Decay" }, { 0, 100, 44, 0, "Mix" }, { 0, 1, 0, 0, "Tail" }, { 0, 0, 0, 0, "-" }, { 0, 0, 0, 0, "-" }, { 0, 0, 0, 0, "-" }, { 0, 0, 0, 0, "-" } } },
  { "PolyOctDw", 111153153, "POCT_DWN.ZD2.BMP", 1, 4, { { 0, 1, 1, 0, "Color" }, { 0, 100, 50, 0, "Tone" }, { 0, 100, 80, 0, "Wet" }, { 0, 100, 80, 0, "Dry" }, { 0, 0, 0, 0, "-" }, { 0, 0, 0, 0, "-" }, { 0, 0, 0, 0, "-" }, { 0, 0, 0, 0, "-" } } },
  { "PolyOctUp", 111153152, "POCT_UP.ZD2.BMP", 1, 4, { { 0, 1, 1, 0, "Color" }, { 0, 100, 50, 0, "Tone" }, { 0, 100, 80, 0, "Wet" }, { 0, 100, 80, 0, "Dry" }, { 0, 0, 0, 0, "-" }, { 0, 0, 0, 0, "-" }, { 0, 0, 0, 0, "-" }, { 0, 0, 0, 0, "-" } } },
  { "P-P Delay", 134217857, "PPDLY_3S.ZD2.BMP", 1, 4, { { 0, 3018, 559, 0, "Time" }, { 0, 100, 30, 0, "F.B" }, { 0, 100, 70, 0, "Mix" }, { 0, 1, 0, 0, "Tail" }, { 0, 0, 0, 0, "-" }, { 0, 0, 0, 0, "-" }, { 0, 0, 0, 0, "-" }, { 0, 0, 0, 0, "-" } } },
  { "Pitch DLY", 134217905, "PTCHDL3S.ZD2.BMP", 1, 4, { { 0, 30, 21, 0, "Pitch" }, { 0, 1999, 89, 0, "Time" }, { 0, 100, 80, 0, "F.B" }, { 0, 100, 80, 0, "Mix" }, { 0, 0, 0, 0, "-" }, { 0, 0, 0, 0, "-" }, { 0, 0, 0, 0, "-" }, { 0, 0, 0, 0, "-" } } },
  { "Tp P.Wah", 195036032, "PWAH_TP.ZD2.BMP", 1, 4, { { 1, 50, 25, 0, "FREQ" }, { 0, 100, 40, 0, "Depth" }, { 0, 10, 5, 0, "Peak" }, { 0, 100, 50, 0, "VOL" }, { 0, 0, 0, 0, "-" }, { 0, 0, 0, 0, "-" }, { 0, 0, 0, 0, "-" }, { 0, 0, 0, 0, "-" } } },
  { "VnDePiezo", 44040838, "PZPREVN.ZD2.BMP", 1, 4, { { 0, 10, 5, 0, "DePZ" }, { 0, 48, 24, 0, "Lo" }, { 0, 48, 24, 0, "Hi" }, { 0, 100, 80, 0, "VOL" }, { 0, 0, 0, 0, "-" }, { 0, 0, 0, 0, "-" }, { 0, 0, 0, 0, "-" }, { 0, 0, 0, 0, "-" } } },
  { "RackComp", 16777248, "RACKCOMP.ZD2.BMP", 1, 4, { { 0, 50, 40, 0, "THRSH" }, { 0, 9, 5, 0, "Ratio" }, { 0, 9, 6, 0, "ATTCK" }, { 0, 100, 80, 0, "VOL" }, { 0, 0, 0, 0, "-" }, { 0, 0, 0, 0, "-" }, { 0, 0, 0, 0, "-" }, { 0, 0, 0, 0, "-" } } },
  { "RC Boost", 50331696, "RCBOOST.ZD2.BMP", 1, 4, { { 0, 100, 58, 0, "Gain" }, { 0, 100, 48, 0, "Bass" }, { 0, 100, 52, 0, "Treble" }, { 0, 100, 48, 0, "VOL" }, { 0, 0, 0, 0, "-" }, { 0, 0, 0, 0, "-" }, { 0, 0, 0, 0, "-" }, { 0, 0, 0, 0, "-" } } },
  { "Resonance", 33554464, "RESONANC.ZD2.BMP", 1, 4, { { 0, 1, 1, 0, "Mode" }, { 0, 9, 4, 0, "Sense" }, { 0, 10, 8, 0, "RESO" }, { 0, 100, 80, 0, "VOL" }, { 0, 0, 0, 0, "-" }, { 0, 0, 0, 0, "-" }, { 0, 0, 0, 0, "-" }, { 0, 0, 0, 0, "-" } } },
  { "RingMod", 100663440, "RINGMOD.ZD2.BMP", 1, 4, { { 0, 49, 27, 0, "FREQ" }, { 0, 10, 10, 0, "Tone" }, { 0, 100, 50, 0, "BAL" }, { 0, 100, 88, 0, "VOL" }, { 0, 0, 0, 0, "-" }, { 0, 0, 0, 0, "-" }, { 0, 0, 0, 0, "-" }, { 0, 0, 0, 0, "-" } } },
  { "RndmFLTR", 33554576, "RNDMFLTR.ZD2.BMP", 1, 4, { { 0, 2, 2, 0, "Type" }, { 0, 77, 34, 0, "Speed" }, { 0, 100, 90, 0, "BAL" }, { 0, 100, 80, 0, "VOL" }, { 0, 0, 0, 0, "-" }, { 0, 0, 0, 0, "-" }, { 0, 0, 0, 0, "-" }, { 0, 0, 0, 0, "-" } } },
  { "RndPhaser", 111153216, "RNDMPHA.ZD2.BMP", 2, 5, { { 0, 3, 0, 0, "Color" }, { 0, 100, 84, 0, "Depth" }, { 0, 100, 46, 0, "RESO" }, { 0, 49, 39, 0, "Range" }, { 0, 4, 2, 0, "INTVL" }, { 0, 0, 0, 0, "-" }, { 0, 0, 0, 0, "-" }, { 0, 0, 0, 0, "-" } } },
  { "Room", 150994976, "ROOM.ZD2.BMP", 1, 4, { { 0, 99, 4, 0, "PreD" }, { 0, 29, 9, 0, "Decay" }, { 0, 100, 60, 0, "Mix" }, { 0, 1, 0, 0, "Tail" }, { 0, 0, 0, 0, "-" }, { 0, 0, 0, 0, "-" }, { 0, 0, 0, 0, "-" }, { 0, 0, 0, 0, "-" } } },
  { "ReverseDL", 134217793, "RVRSDL3S.ZD2.BMP", 1, 4, { { 0, 1503, 990, 0, "Time" }, { 0, 100, 20, 0, "F.B" }, { 0, 100, 50, 0, "BAL" }, { 0, 1, 0, 0, "Tail" }, { 0, 0, 0, 0, "-" }, { 0, 0, 0, 0, "-" }, { 0, 0, 0, 0, "-" }, { 0, 0, 0, 0, "-" } } },
  { "SeqFLTR", 33554496, "SEQFLTR.ZD2.BMP", 1, 4, { { 0, 6, 6, 0, "Step" }, { 0, 7, 6, 0, "PTTRN" }, { 0, 77, 25, 0, "Speed" }, { 0, 10, 10, 0, "RESO" }, { 0, 0, 0, 0, "-" }, { 0, 0, 0, 0, "-" }, { 0, 0, 0, 0, "-" }, { 0, 0, 0, 0, "-" } } },
  { "SlwAtkDly", 134218001, "SLATDL3S.ZD2.BMP", 1, 4, { { 0, 49, 24, 0, "Swell" }, { 0, 1411, 489, 0, "Time" }, { 0, 100, 71, 0, "F.B" }, { 0, 100, 64, 0, "Mix" }, { 0, 0, 0, 0, "-" }, { 0, 0, 0, 0, "-" }, { 0, 0, 0, 0, "-" }, { 0, 0, 0, 0, "-" } } },
  { "Slicer", 100663536, "SLICER.ZD2.BMP", 1, 4, { { 0, 19, 0, 0, "PTTRN" }, { 0, 77, 24, 0, "Speed" }, { 0, 50, 20, 0, "THRSH" }, { 0, 100, 87, 0, "VOL" }, { 0, 0, 0, 0, "-" }, { 0, 0, 0, 0, "-" }, { 0, 0, 0, 0, "-" }, { 0, 0, 0, 0, "-" } } },
  { "SlapBackD", 134217921, "SLPBKD3S.ZD2.BMP", 1, 4, { { 0, 300, 98, 0, "Time" }, { 0, 100, 29, 0, "F.B" }, { 0, 100, 40, 0, "Mix" }, { 0, 2, 0, 0, "SubDv" }, { 0, 0, 0, 0, "-" }, { 0, 0, 0, 0, "-" }, { 0, 0, 0, 0, "-" }, { 0, 0, 0, 0, "-" } } },
  { "SlowATTCK", 16777264, "SLWATK.ZD2.BMP", 1, 4, { { 0, 49, 20, 0, "Time" }, { 0, 10, 10, 0, "Curve" }, { 0, 100, 100, 0, "Tone" }, { 0, 100, 80, 0, "VOL" }, { 0, 0, 0, 0, "-" }, { 0, 0, 0, 0, "-" }, { 0, 0, 0, 0, "-" }, { 0, 0, 0, 0, "-" } } },
  { "SoftEcho", 134218017, "SOFTEC3S.ZD2.BMP", 1, 4, { { 0, 1, 1, 0, "MOD" }, { 0, 562, 387, 0, "Time" }, { 0, 100, 47, 0, "F.B" }, { 0, 100, 69, 0, "Mix" }, { 0, 0, 0, 0, "-" }, { 0, 0, 0, 0, "-" }, { 0, 0, 0, 0, "-" }, { 0, 0, 0, 0, "-" } } },
  { "Splitter", 41943168, "SPLITTER.ZD2.BMP", 1, 4, { { 0, 15, 2, 0, "FREQ" }, { 0, 50, 16, 0, "Lo" }, { 0, 50, 19, 0, "Hi" }, { 0, 100, 80, 0, "VOL" }, { 0, 0, 0, 0, "-" }, { 0, 0, 0, 0, "-" }, { 0, 0, 0, 0, "-" }, { 0, 0, 0, 0, "-" } } },
  { "Spring", 150995024, "SPRING.ZD2.BMP", 1, 4, { { 0, 99, 0, 0, "PreD" }, { 0, 29, 19, 0, "Decay" }, { 0, 100, 50, 0, "Mix" }, { 0, 1, 0, 0, "Tail" }, { 0, 0, 0, 0, "-" }, { 0, 0, 0, 0, "-" }, { 0, 0, 0, 0, "-" }, { 0, 0, 0, 0, "-" } } },
  { "St Ba GEQ", 41943137, "STBGEQ1U.ZD2.BMP", 2, 8, { { 0, 48, 24, 0, "50" }, { 0, 48, 24, 0, "120" }, { 0, 48, 24, 0, "400" }, { 0, 48, 24, 0, "500" }, { 0, 48, 24, 0, "800" }, { 0, 48, 24, 0, "4.5k" }, { 0, 48, 24, 0, "10k" }, { 0, 100, 80, 0, "VOL" } } },
  { "StdSyn", 125829136, "STDSYN.ZD2.BMP", 1, 4, { { 0, 100, 10, 0, "Sense" }, { 0, 3, 0, 0, "Sound" }, { 0, 10, 7, 0, "Tone" }, { 0, 100, 50, 0, "BAL" }, { 0, 0, 0, 0, "-" }, { 0, 0, 0, 0, "-" }, { 0, 0, 0, 0, "-" }, { 0, 0, 0, 0, "-" } } },
  { "Step", 33554624, "STEP.ZD2.BMP", 1, 4, { { 0, 100, 60, 0, "Depth" }, { 0, 78, 25, 0, "Rate" }, { 0, 10, 8, 0, "RESO" }, { 0, 10, 10, 0, "Shape" }, { 0, 0, 0, 0, "-" }, { 0, 0, 0, 0, "-" }, { 0, 0, 0, 0, "-" }, { 0, 0, 0, 0, "-" } } },
  { "StereoCho", 100663344, "STEREOCH.ZD2.BMP", 1, 4, { { 0, 100, 80, 0, "Depth" }, { 0, 49, 29, 0, "Rate" }, { 0, 10, 7, 0, "Tone" }, { 0, 100, 60, 0, "Mix" }, { 0, 0, 0, 0, "-" }, { 0, 0, 0, 0, "-" }, { 0, 0, 0, 0, "-" }, { 0, 0, 0, 0, "-" } } },
  { "St Gt GEQ", 33554529, "STGTGE1U.ZD2.BMP", 2, 7, { { 0, 48, 24, 0, "160" }, { 0, 48, 24, 0, "400" }, { 0, 48, 24, 0, "800" }, { 0, 48, 24, 0, "3.2k" }, { 0, 48, 24, 0, "6.4k" }, { 0, 48, 24, 0, "12k" }, { 0, 100, 80, 0, "VOL" }, { 0, 0, 0, 0, "-" } } },
  { "StonePha", 100663584, "STONEPHA.ZD2.BMP", 1, 4, { { 0, 1, 0, 0, "Color" }, { 0, 100, 100, 0, "Depth" }, { 0, 100, 50, 0, "Rate" }, { 0, 100, 40, 0, "RESO" }, { 0, 0, 0, 0, "-" }, { 0, 0, 0, 0, "-" }, { 0, 0, 0, 0, "-" }, { 0, 0, 0, 0, "-" } } },
  { "SuperCho", 100663568, "SUPERCHO.ZD2.BMP", 1, 4, { { 0, 100, 50, 0, "Depth" }, { 0, 100, 50, 0, "Rate" }, { 0, 100, 50, 0, "Tone" }, { 0, 100, 42, 0, "Mix" }, { 0, 0, 0, 0, "-" }, { 0, 0, 0, 0, "-" }, { 0, 0, 0, 0, "-" }, { 0, 0, 0, 0, "-" } } },
  { "SynTlk", 125829152, "SYNTLK.ZD2.BMP", 1, 4, { { 0, 100, 40, 0, "Decay" }, { 0, 3, 1, 0, "Type" }, { 0, 10, 8, 0, "Tone" }, { 0, 100, 50, 0, "BAL" }, { 0, 0, 0, 0, "-" }, { 0, 0, 0, 0, "-" }, { 0, 0, 0, 0, "-" }, { 0, 0, 0, 0, "-" } } },
  { "TapeEcho", 134217776, "TAPEECHO.ZD2.BMP", 1, 4, { { 0, 2014, 559, 0, "Time" }, { 0, 100, 64, 0, "F.B" }, { 0, 100, 56, 0, "Mix" }, { 0, 1, 0, 0, "Tail" }, { 0, 0, 0, 0, "-" }, { 0, 0, 0, 0, "-" }, { 0, 0, 0, 0, "-" }, { 0, 0, 0, 0, "-" } } },
  { "TheVibe", 100663392, "THEVIBE.ZD2.BMP", 1, 4, { { 0, 50, 25, 0, "Speed" }, { 0, 100, 60, 0, "Depth" }, { 0, 1, 1, 0, "Mode" }, { 0, 100, 80, 0, "VOL" }, { 0, 0, 0, 0, "-" }, { 0, 0, 0, 0, "-" }, { 0, 0, 0, 0, "-" }, { 0, 0, 0, 0, "-" } } },
  { "TapeEcho3", 134217969, "TPEC3_3S.ZD2.BMP", 2, 8, { { 0, 100, 50, 0, "Gain" }, { 0, 100, 62, 0, "Hi" }, { 0, 100, 47, 0, "Lo" }, { 0, 100, 80, 0, "VOL" }, { 0, 1005, 350, 0, "Time" }, { 0, 100, 20, 0, "F.B" }, { 0, 100, 50, 0, "Mix" }, { 0, 100, 50, 0, "RecLv" } } },
  { "Tremolo", 100663312, "TREMOLO.ZD2.BMP", 1, 4, { { 0, 2, 0, 0, "Wave" }, { 0, 100, 90, 0, "Depth" }, { 0, 110, 50, 0, "Rate" }, { 0, 100, 62, 0, "VOL" }, { 0, 0, 0, 0, "-" }, { 0, 0, 0, 0, "-" }, { 0, 0, 0, 0, "-" }, { 0, 0, 0, 0, "-" } } },
  { "TS Drive", 50331664, "TS_DRIVE.ZD2.BMP", 1, 4, { { 0, 100, 74, 0, "Gain" }, { 0, 1, 0, 0, "Boost" }, { 0, 100, 57, 0, "Tone" }, { 0, 100, 82, 0, "VOL" }, { 0, 0, 0, 0, "-" }, { 0, 0, 0, 0, "-" }, { 0, 0, 0, 0, "-" }, { 0, 0, 0, 0, "-" } } },
  { "Vibrato", 100663408, "VIBRATO.ZD2.BMP", 1, 4, { { 0, 100, 40, 0, "Depth" }, { 0, 78, 30, 0, "Rate" }, { 0, 10, 7, 0, "Tone" }, { 0, 100, 72, 0, "BAL" }, { 0, 0, 0, 0, "-" }, { 0, 0, 0, 0, "-" }, { 0, 0, 0, 0, "-" }, { 0, 0, 0, 0, "-" } } },
  { "VinFLNGR", 100663376, "VINFLNGR.ZD2.BMP", 1, 4, { { 0, 50, 4, 0, "PreD" }, { 0, 100, 47, 0, "Depth" }, { 0, 78, 7, 0, "Rate" }, { 0, 20, 18, 0, "RESO" }, { 0, 0, 0, 0, "-" }, { 0, 0, 0, 0, "-" }, { 0, 0, 0, 0, "-" }, { 0, 0, 0, 0, "-" } } },
  { "VoiceWah", 184549584, "VOICE_WH.ZD2.BMP", 1, 4, { { 1, 100, 0, 0, "Vowel" }, { 0, 2, 1, 0, "PTTRN" }, { 0, 100, 50, 0, "Voice" }, { 0, 1, 0, 0, "Mode" }, { 0, 0, 0, 0, "-" }, { 0, 0, 0, 0, "-" }, { 0, 0, 0, 0, "-" }, { 0, 0, 0, 0, "-" } } },
  { "WAH100", 184549440, "WH100.ZD2.BMP", 1, 4, { { 1, 50, 25, 0, "FREQ" }, { 0, 100, 40, 0, "Depth" }, { 0, 100, 0, 0, "Dry" }, { 0, 100, 80, 0, "VOL" }, { 0, 0, 0, 0, "-" }, { 0, 0, 0, 0, "-" }, { 0, 0, 0, 0, "-" }, { 0, 0, 0, 0, "-" } } },
  { "WarpPhase", 100663648, "WRPPHASE.ZD2.BMP", 1, 4, { { 0, 1, 0, 0, "Mode" }, { 0, 77, 24, 0, "Speed" }, { 0, 10, 7, 0, "RESO" }, { 0, 100, 80, 0, "VOL" }, { 0, 0, 0, 0, "-" }, { 0, 0, 0, 0, "-" }, { 0, 0, 0, 0, "-" }, { 0, 0, 0, 0, "-" } } },
  { "ZNR", 16777280, "ZNR.ZD2.BMP", 1, 4, { { 0, 1, 1, 0, "DETCT" }, { 0, 100, 100, 0, "Depth" }, { 0, 100, 30, 0, "THRSH" }, { 0, 100, 0, 0, "Decay" }, { 0, 0, 0, 0, "-" }, { 0, 0, 0, 0, "-" }, { 0, 0, 0, 0, "-" }, { 0, 0, 0, 0, "-" } } },
  { "Z-Syn", 125829169, "Z_SYN_1U.ZD2.BMP", 2, 8, { { 0, 10, 2, 0, "FREQ" }, { 0, 20, 8, 0, "Range" }, { 0, 100, 72, 0, "Decay" }, { 0, 20, 18, 0, "RESO" }, { 0, 1, 0, 0, "Wave" }, { 0, 10, 7, 0, "Tone" }, { 0, 100, 80, 0, "BAL" }, { 0, 100, 80, 0, "VOL" } } },
  { "Z Tron", 41943072, "Z_TRON.ZD2.BMP", 1, 4, { { 0, 19, 16, 0, "Sense" }, { 0, 10, 7, 0, "RESO" }, { 0, 100, 25, 0, "Dry" }, { 0, 100, 83, 0, "VOL" }, { 0, 0, 0, 0, "-" }, { 0, 0, 0, 0, "-" }, { 0, 0, 0, 0, "-" }, { 0, 0, 0, 0, "-" } } }
};

#define N_X_PEDALS 21

long xpedal_ids[] = { 192938000, 184549408, 192938048, 192938032, 184549424, 184549569, 184549537, 184549601, 184549616, 184549504, 184549632, 184549472, 184549520, 184549456, 192938016, 184549552, 184549488, 184549392, 195036032, 184549584, 184549440 };

#endif
